Resaj/Temporizador/images/IMG_20170706_131056.jpg

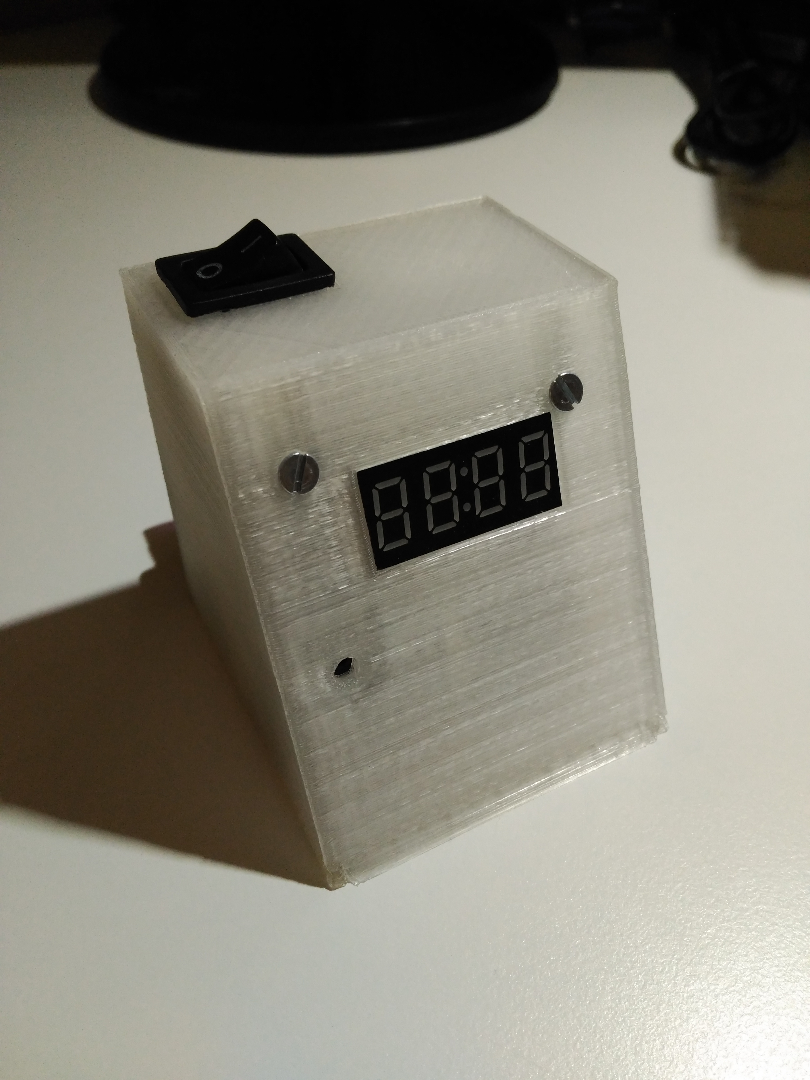
images/IMG_20170706_131056.jpg
