Resaj/Temporizador/images/IMG_20170706_131133.jpg

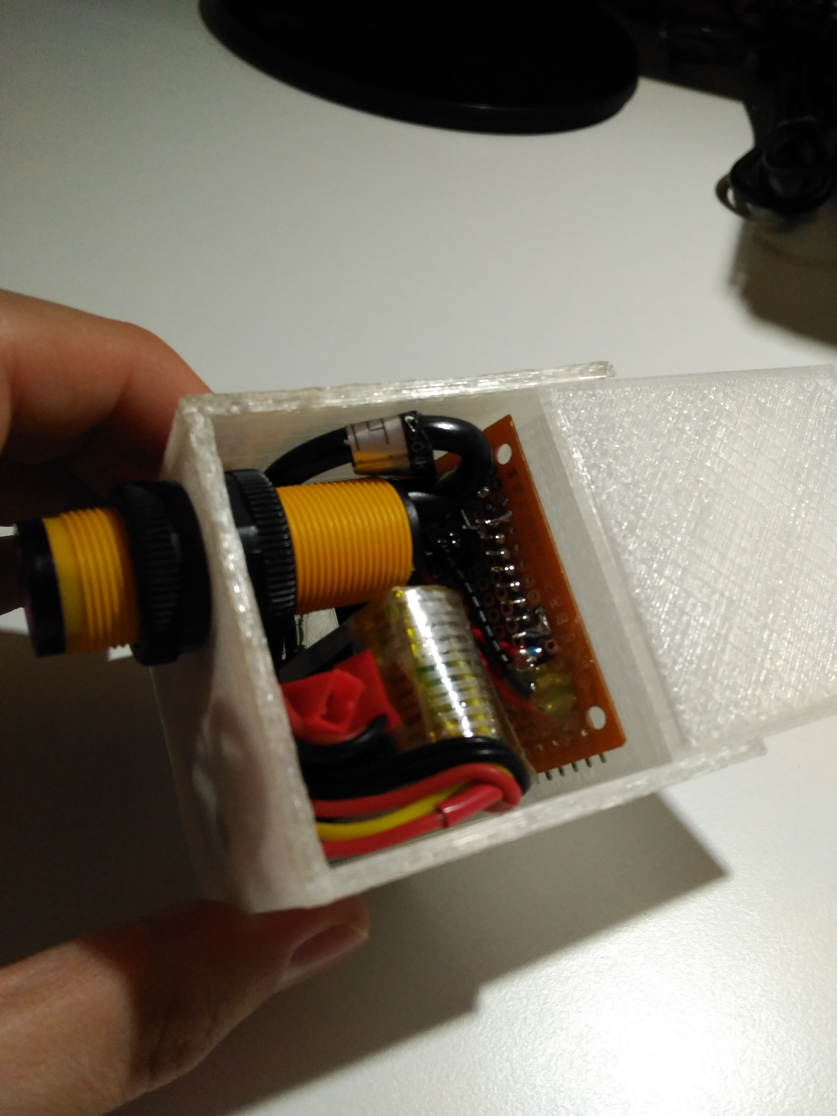
images/IMG_20170706_131133.jpg
