Resaj/Temporizador/images/IMG_20170706_131159.jpg

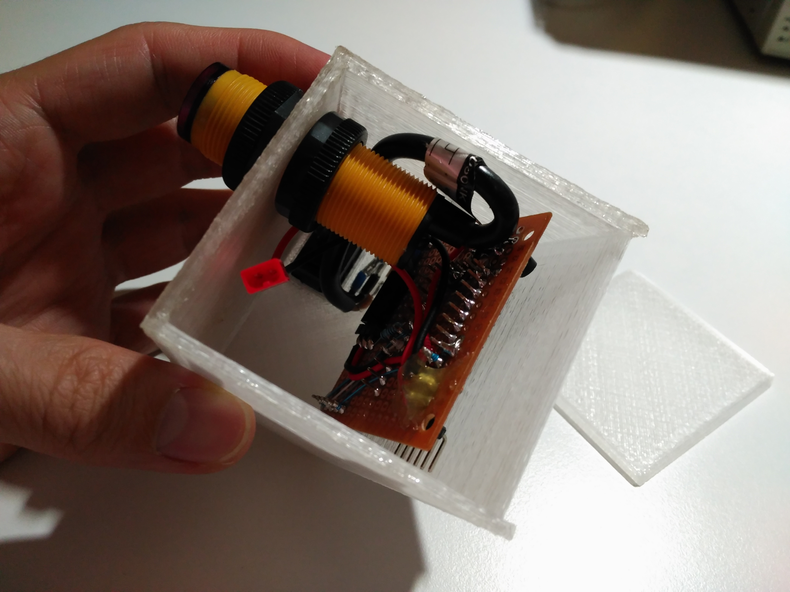
images/IMG_20170706_131159.jpg
