Resaj/Temporizador/images/IMG_20170706_131237.jpg

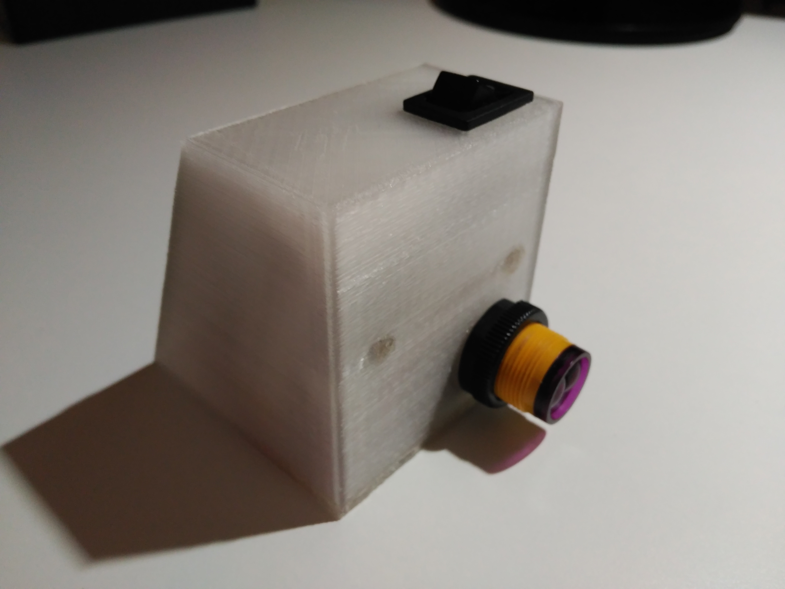
images/IMG_20170706_131237.jpg
